hixfield/HixPower/doc/buyonebay.jpg

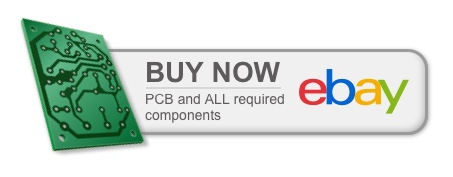
doc/buyonebay.jpg
