hixfield/HixPower/hardware/images/1206_led_red.jpg

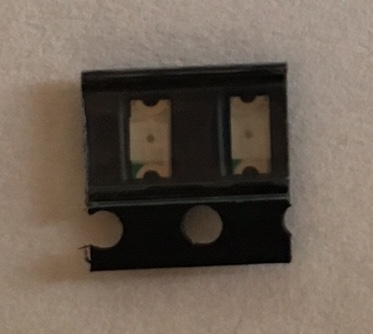
hardware/images/1206_led_red.jpg
