hixfield/HixPower/hardware/images/1206_res_2.2k.jpg

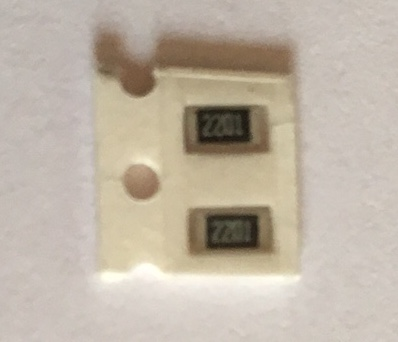
hardware/images/1206_res_2.2k.jpg
