hixfield/HixPower/hardware/images/1206_res_4.7k.jpg

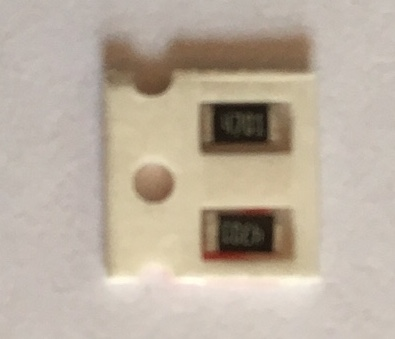
hardware/images/1206_res_4.7k.jpg
