hixfield/HixPower/hardware/images/1206_res_10k.jpg

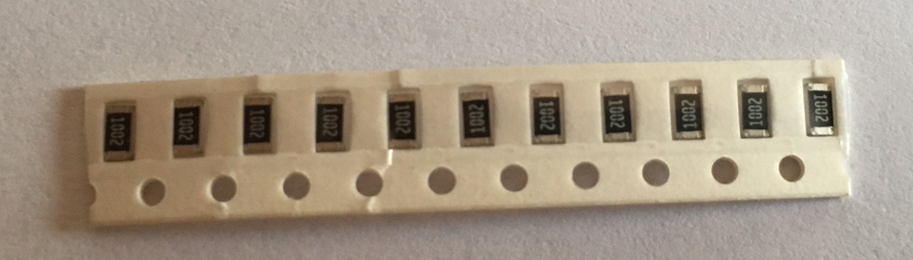
hardware/images/1206_res_10k.jpg
