hixfield/HixPower/hardware/images/1206_res_330.jpg

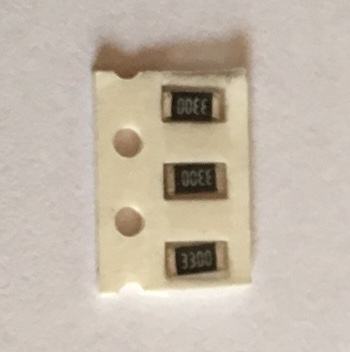
hardware/images/1206_res_330.jpg
