hixfield/HixPower/hardware/images/cablelugforkm4.jpg

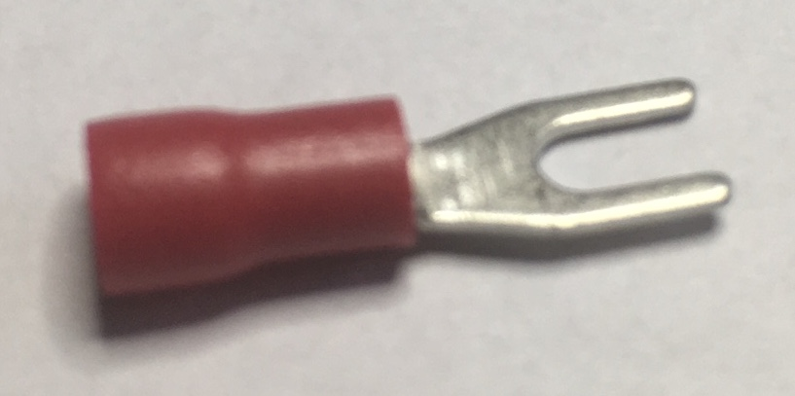
hardware/images/cablelugforkm4.jpg
