hixfield/HixPower/hardware/images/cablelugroundm3.jpg

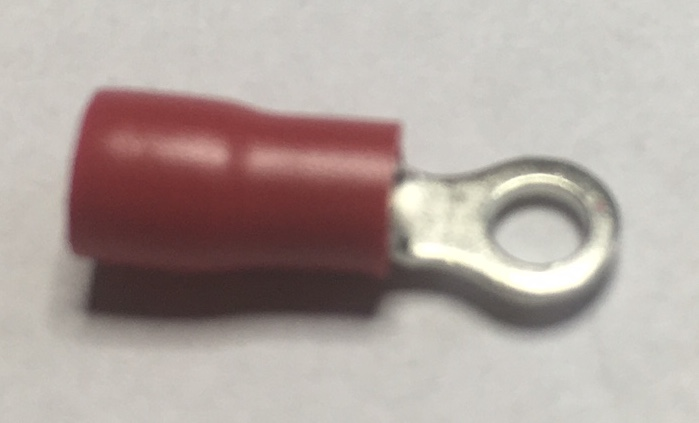
hardware/images/cablelugroundm3.jpg
