hixfield/HixPower/hardware/images/case.jpg

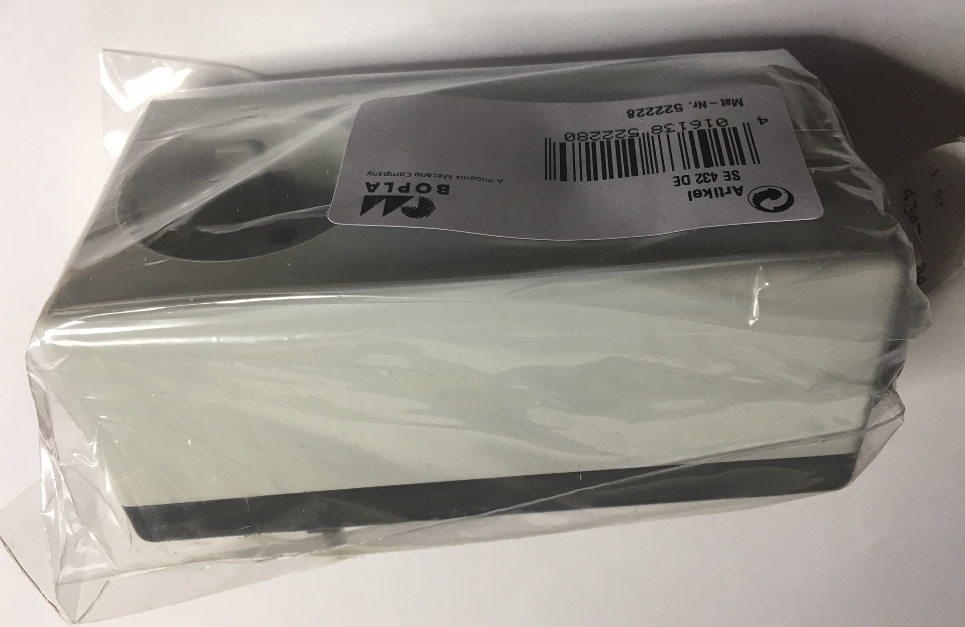
hardware/images/case.jpg
