hixfield/HixPower/hardware/images/ds18b20.jpg

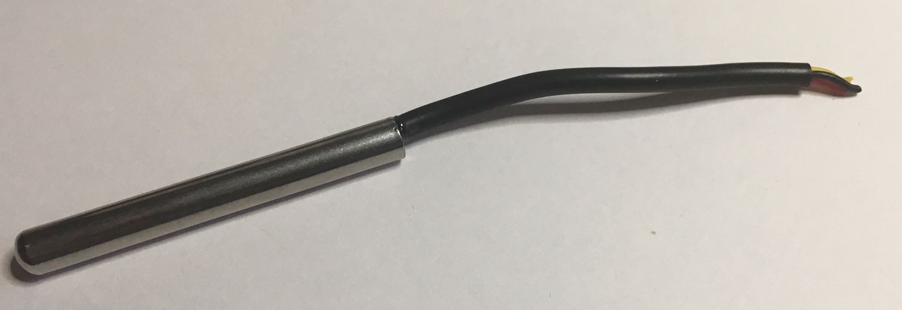
hardware/images/ds18b20.jpg
