hixfield/HixPower/hardware/images/esp12e.jpg

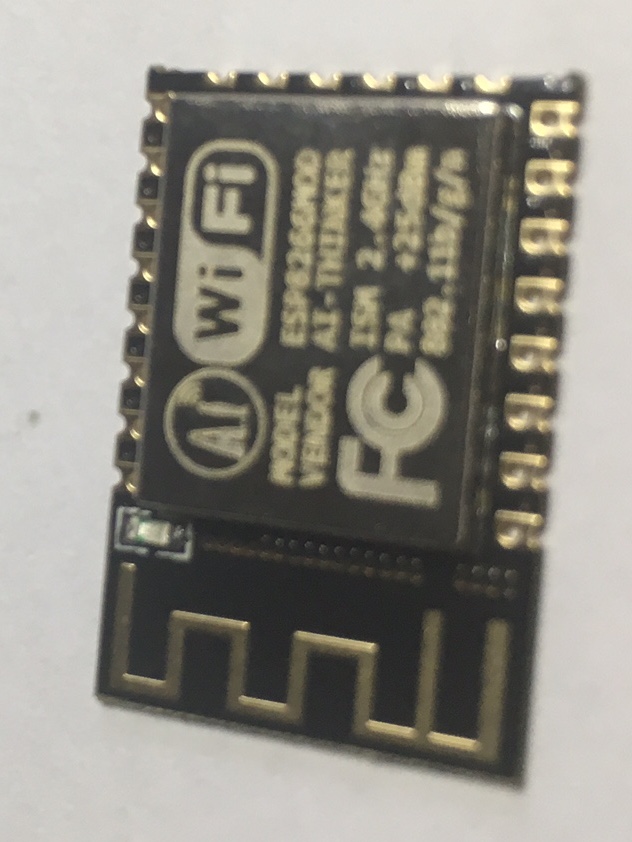
hardware/images/esp12e.jpg
