hixfield/HixPower/hardware/images/mainswire.JPG

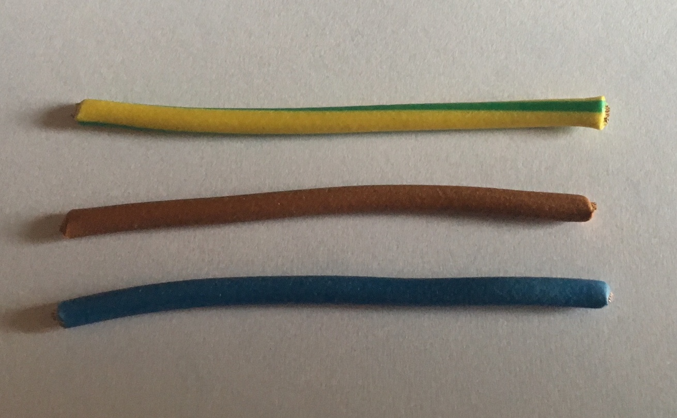
hardware/images/mainswire.JPG
