hixfield/HixPower/hardware/images/micropushbutton.jpg

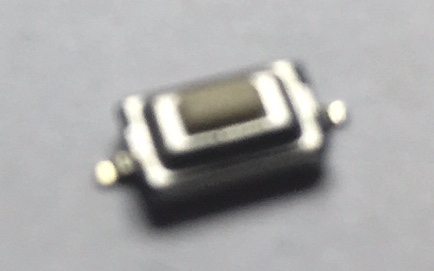
hardware/images/micropushbutton.jpg
