hixfield/HixPower/hardware/images/pcbbottom.jpg

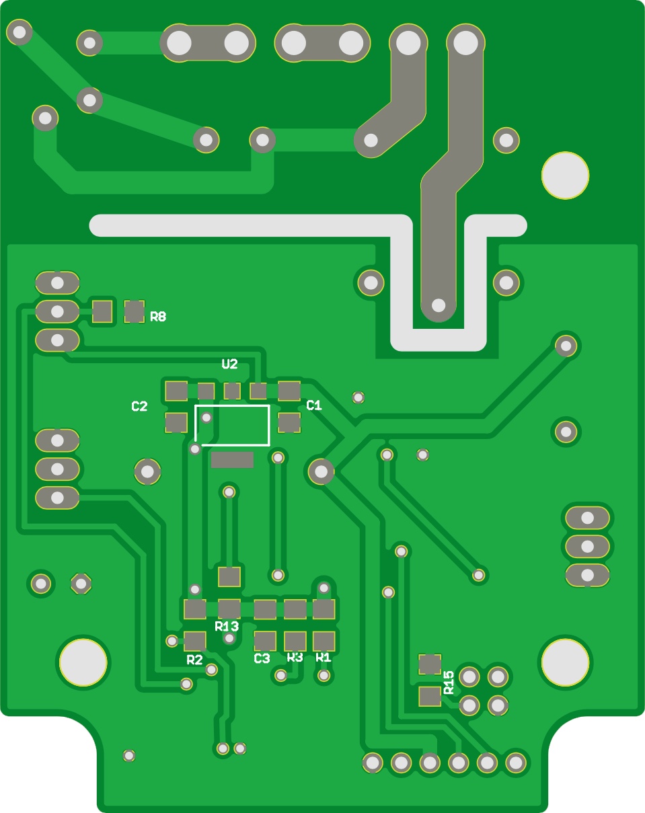
hardware/images/pcbbottom.jpg
