hixfield/HixPower/hardware/images/pirmodule.jpg

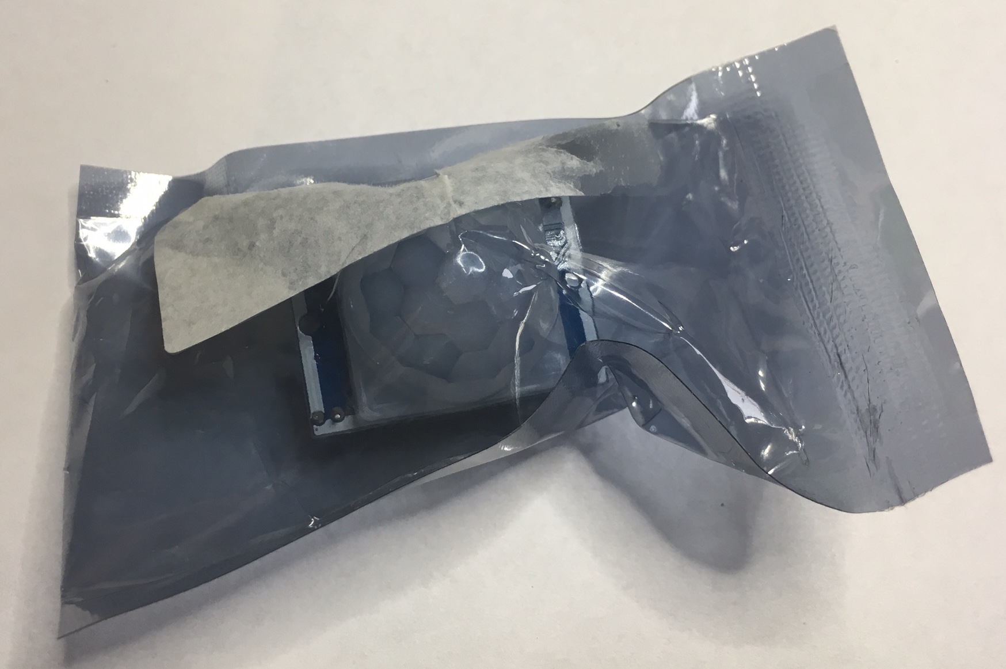
hardware/images/pirmodule.jpg
