hixfield/HixPower/hardware/images/pushbutton.jpg

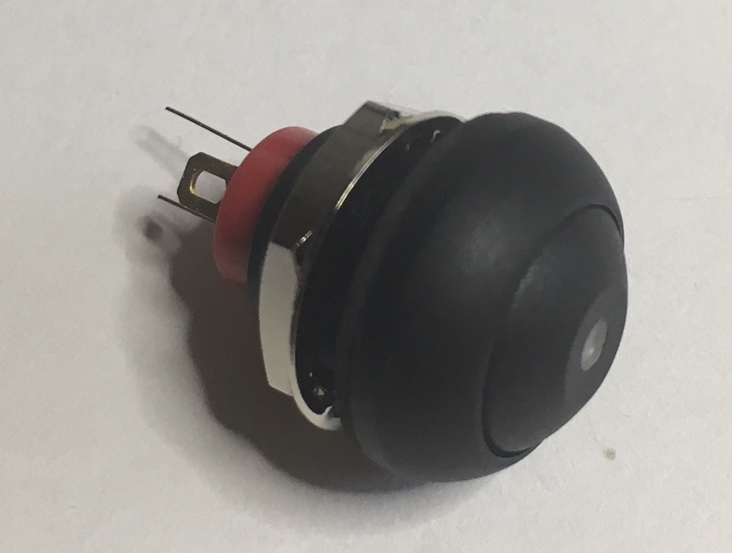
hardware/images/pushbutton.jpg
