hixfield/HixPower/hardware/images/relay.jpg

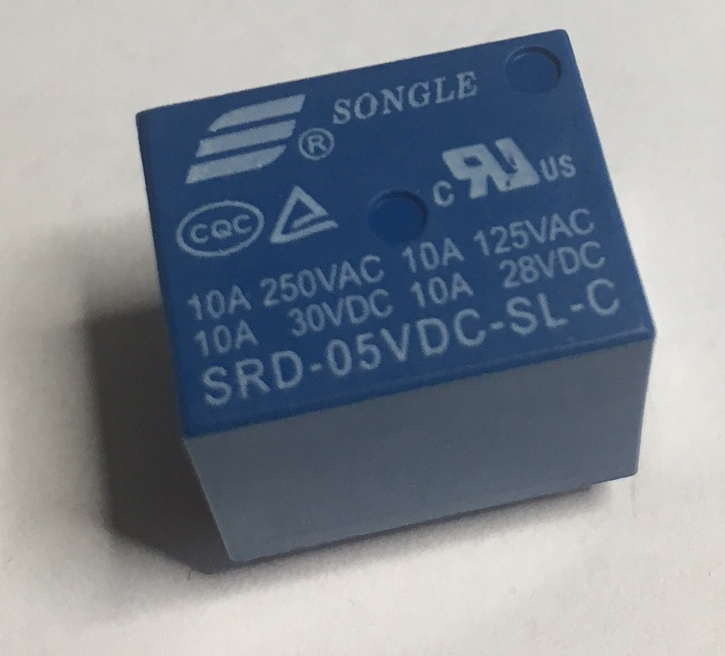
hardware/images/relay.jpg
