hixfield/HixPower/hardware/images/screw.jpg

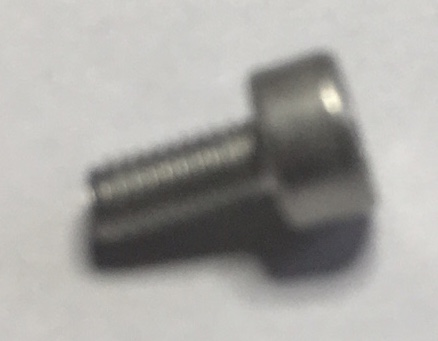
hardware/images/screw.jpg
