hixfield/HixPower/hardware/images/sod80_bav103.jpg

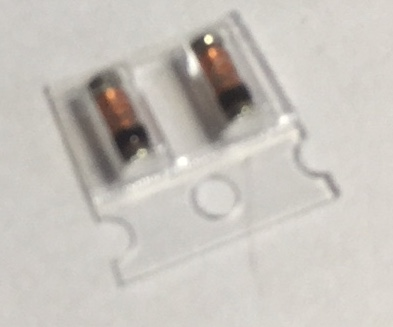
hardware/images/sod80_bav103.jpg
