hixfield/HixPower/hardware/images/sot23_bc847c.jpg

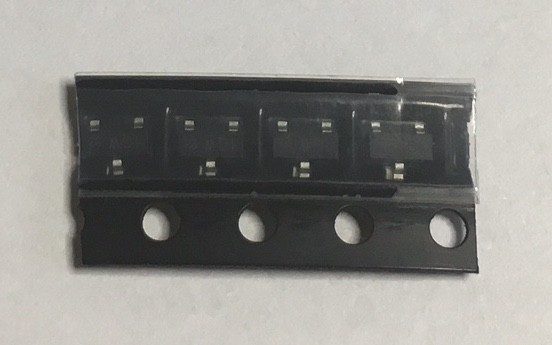
hardware/images/sot23_bc847c.jpg
