hixfield/HixPower/hardware/images/sot223_lm3940.jpg

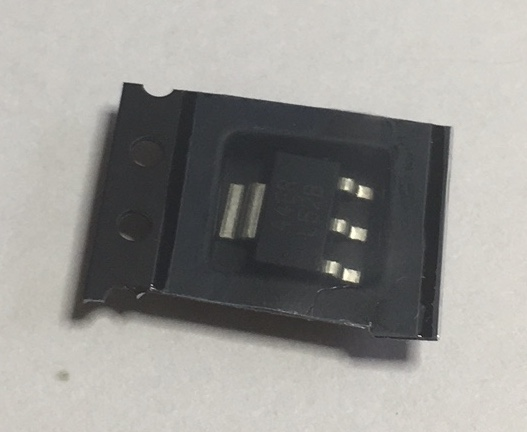
hardware/images/sot223_lm3940.jpg
