hixfield/HixPower/hardware/images/th_cap.jpg

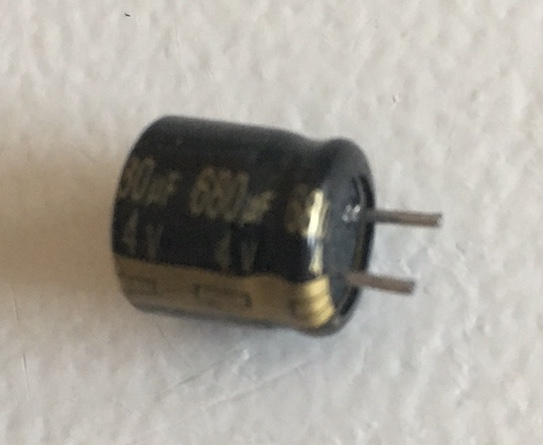
hardware/images/th_cap.jpg
