hixfield/HixPower/hardware/images/th_ftdi.jpg

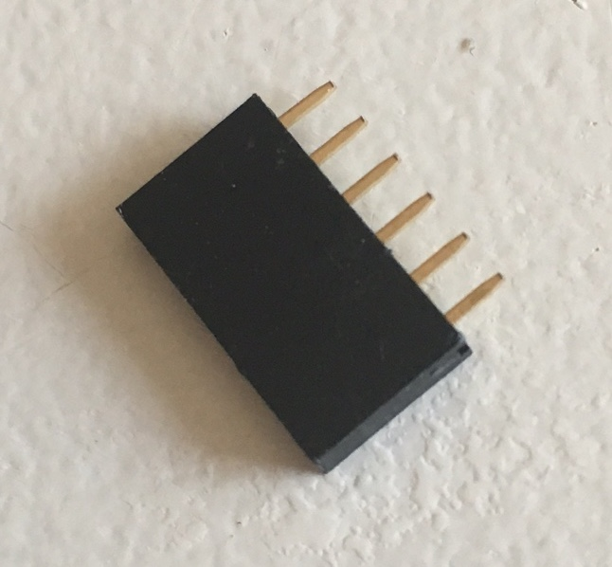
hardware/images/th_ftdi.jpg
