hixfield/HixPower/hardware/images/th_hlk-pm01.jpg

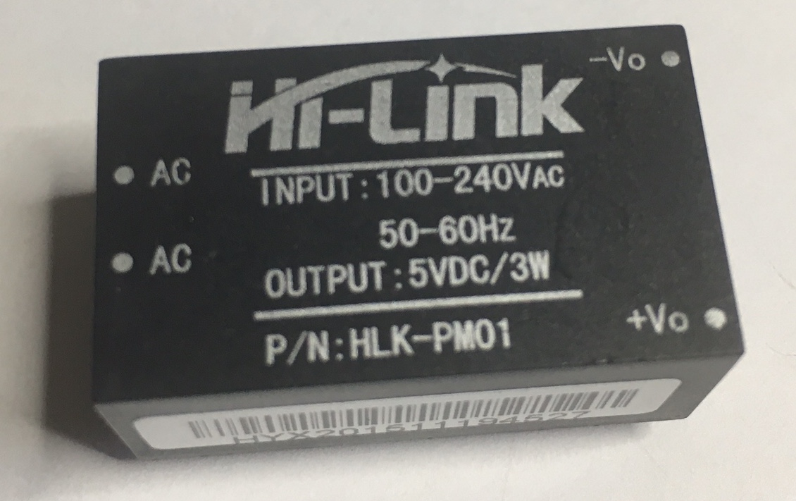
hardware/images/th_hlk-pm01.jpg
