hixfield/HixPower/hardware/images/th_s10k275.jpg

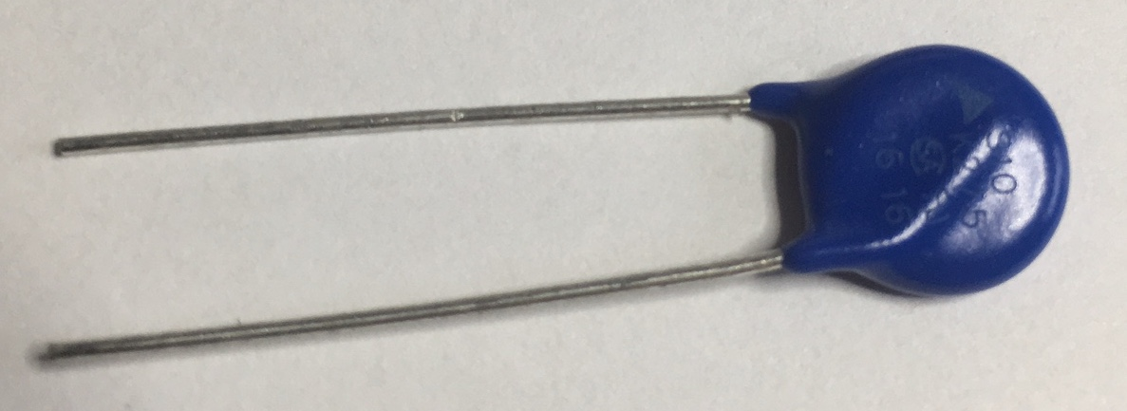
hardware/images/th_s10k275.jpg
