hixfield/HixPower/hardware/images/th_xh3pmale.jpg

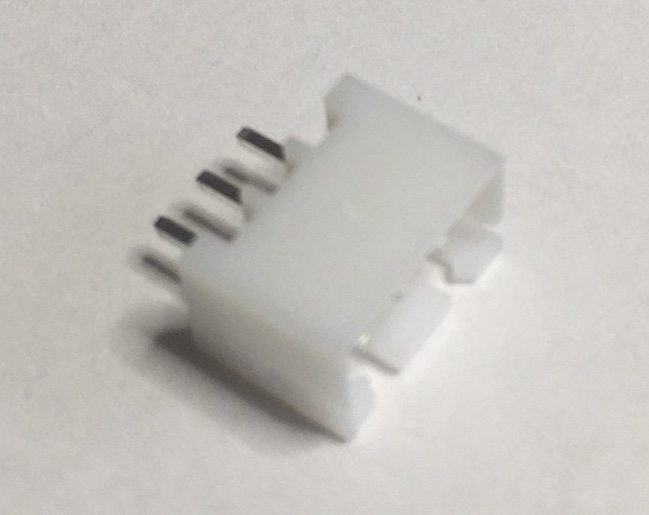
hardware/images/th_xh3pmale.jpg
