hixfield/HixPower/software/doc/high-voltage.png

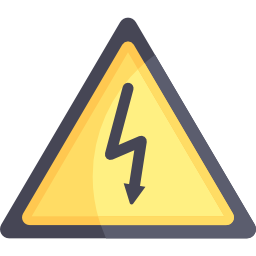
software/doc/high-voltage.png
