hixfield/HixPower/hardware/images/xh3pfemalesolder.jpg

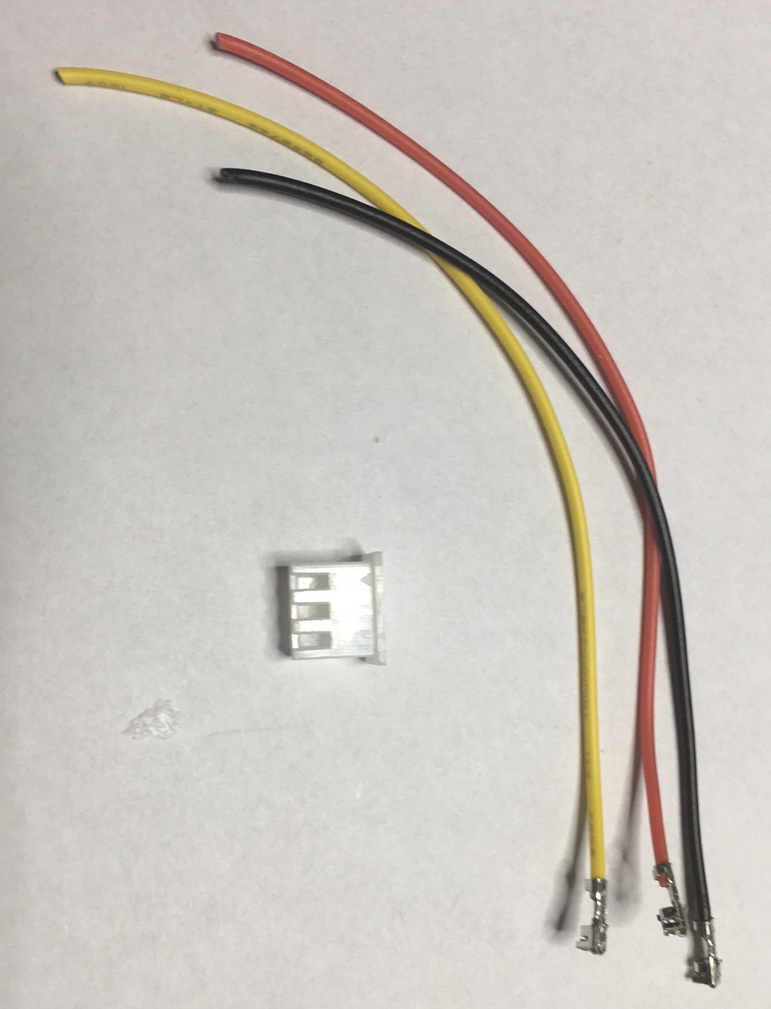
hardware/images/xh3pfemalesolder.jpg
