hixfield/HixPower/software/src/HixMQTT.h

#ifndef HixMQTT_h
#define HixMQTT_h

#include "HixConfig.h"
#include <HixMQTTBase.h>

class HixMQTT : public HixMQTTBase {
  private:
    //link to the configuration
    HixConfig & m_config;
    //puts all values in one single json compatible with influxDB
    String influxDBJson(float         fTemperature,
                        bool          bMotionDetected,
                        bool          bSwitchPressed,
                        bool          bBeeperOn,
                        bool          bOutputAllowed,
                        bool          bOutputOn,
                        unsigned long nSecondsLeft);

  public:
    HixMQTT(HixConfig &  config,
            const char * szWifi_SSID,
            const char * szWiFi_Password,
            const char * szMQTT_Server,
            const char * szDeviceType,
            const char * szDeviceVersion,
            const char * szRoom,
            const char * szDeviceTag,
            const char * szDeviceBuildTimestamp);
    //publishes all the values for the sensor
    bool publishStatusValues(float         fTemperature,
                             bool          bMotionDetected,
                             bool          bSwitchPressed,
                             bool          bBeeperOn,
                             bool          bOutputAllowed,
                             bool          bOutputOn,
                             unsigned long nSecondsLeft);
    bool publishDeviceValues(void);
};

#endif
